vk2diy/adxi/doc/filter-models/bandpass-filter/README.md

# Bandpass Filter

This is a model of the bandpass filter immediately after the PC audio input.

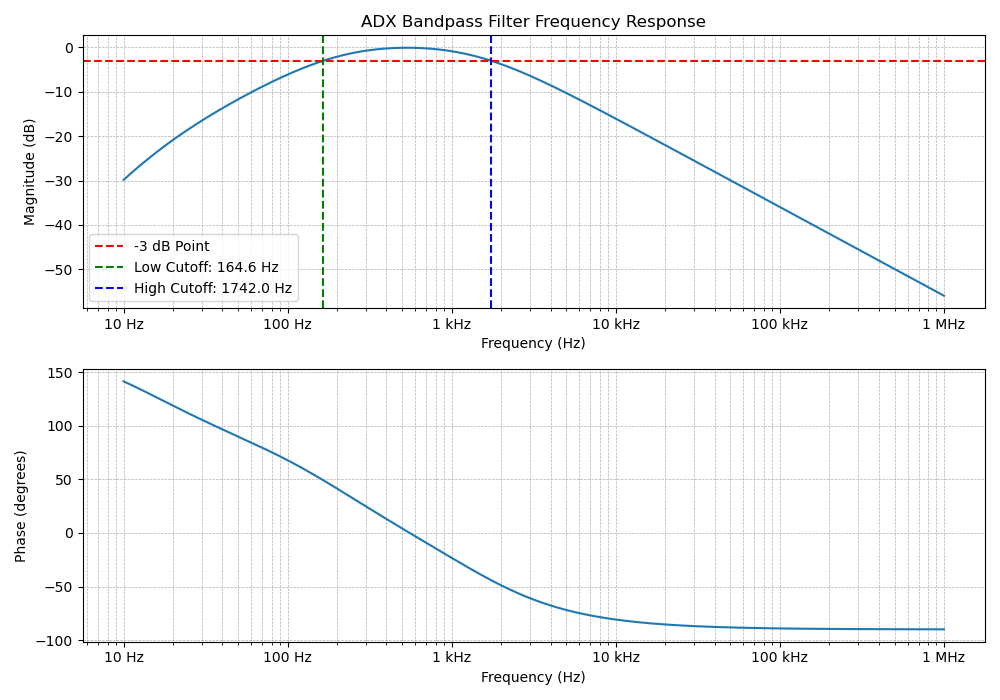
[picture p105: doc/filter-models/bandpass-filter/bandpass-filter-model.png]


Its accuracy is unknown.
