vk2diy/adxi/images/prototype-late-stage-module-2.webp

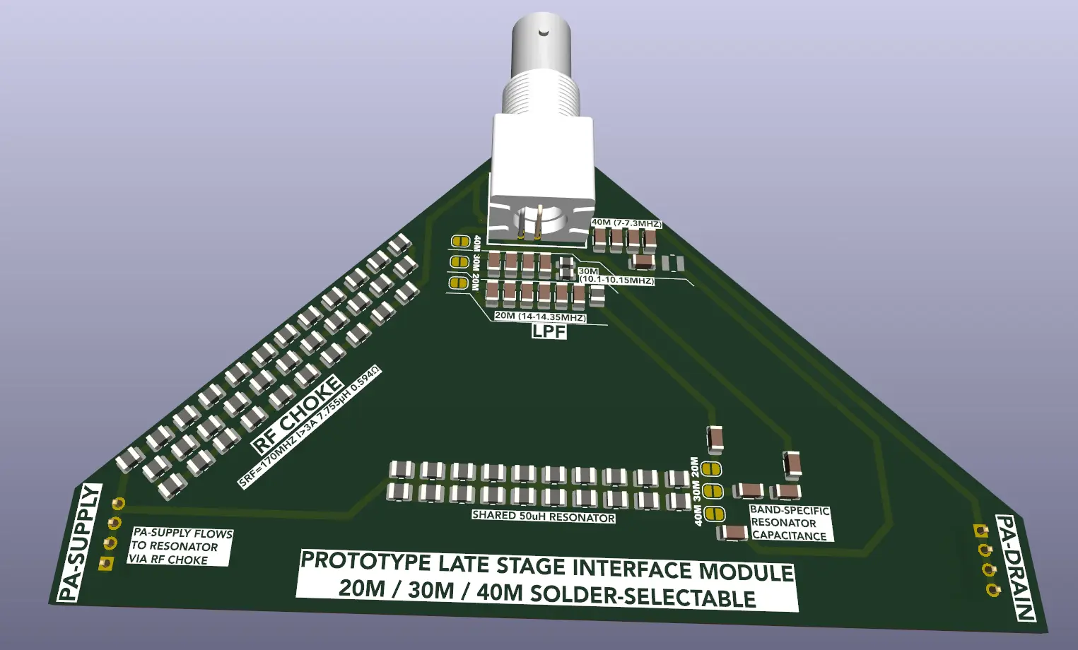
images/prototype-late-stage-module-2.webp
